busbuyukefe/efesonik/screenshots/2021-02-08-214756_1440x900_scrot.png

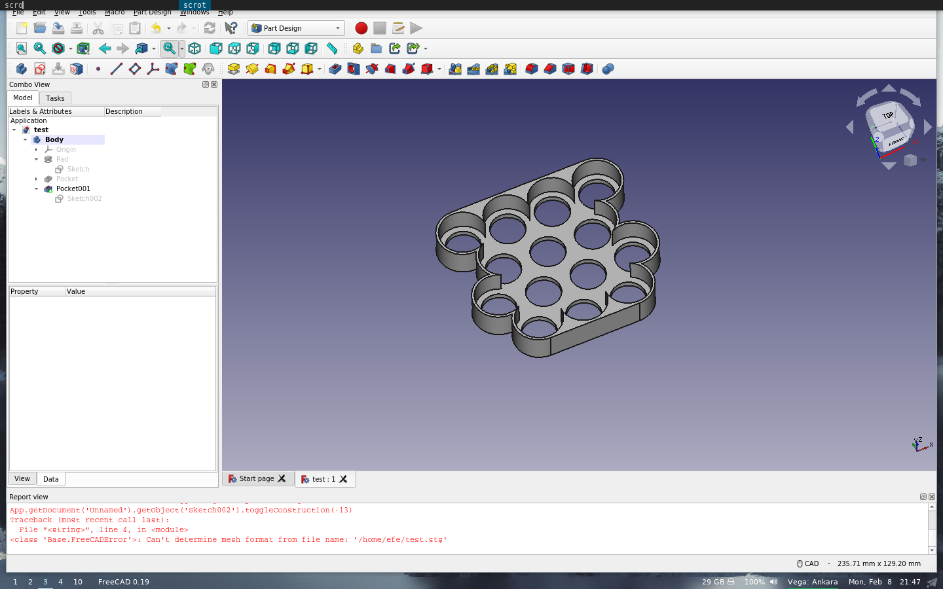
screenshots/2021-02-08-214756_1440x900_scrot.png
